pyroesp/PlayStation-1-Reset-Mod/pictures/arduino nano/arduino nano bottom.jpg

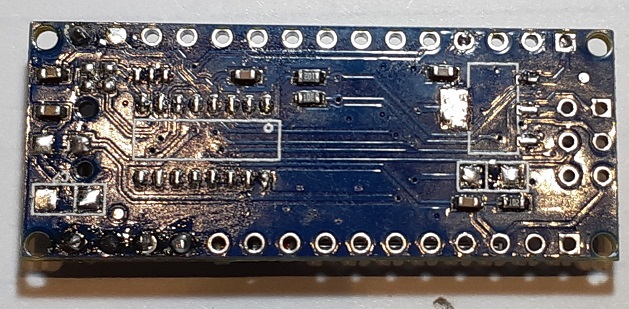
pictures/arduino nano/arduino nano bottom.jpg
