pyroesp/PlayStation-1-Reset-Mod/pictures/arduino nano/arduino nano top.jpg

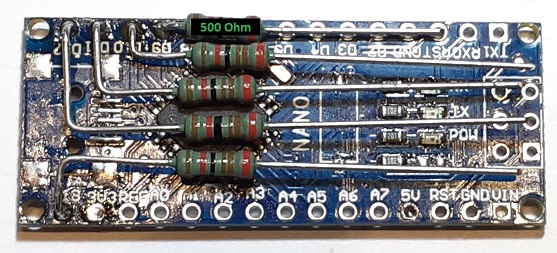
pictures/arduino nano/arduino nano top.jpg
