pyroesp/PlayStation-1-Reset-Mod/pictures/arduino nano/playstation with mod 2.jpg

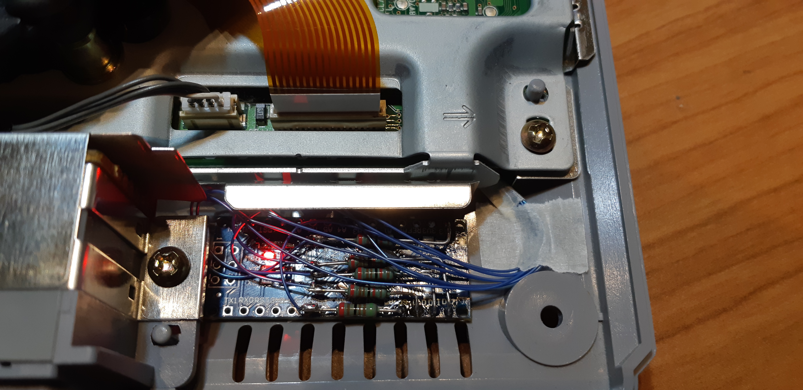
pictures/arduino nano/playstation with mod 2.jpg
