pyroesp/PlayStation-1-Reset-Mod/pictures/arduino nano/playstation with mod.jpg

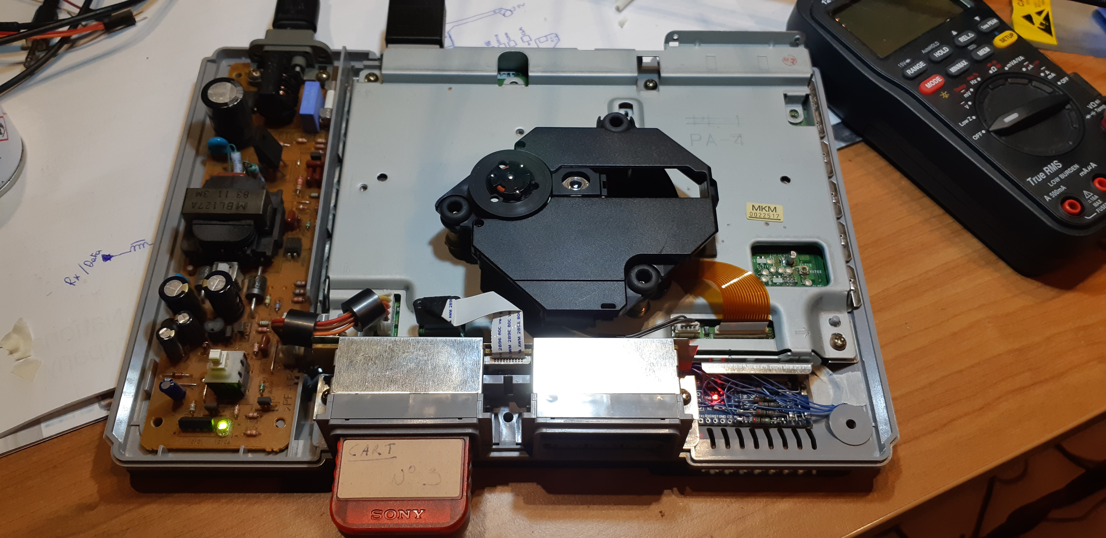
pictures/arduino nano/playstation with mod.jpg
