pyroesp/PlayStation-1-Reset-Mod/pictures/arduino nano/reset from parallel port.jpg

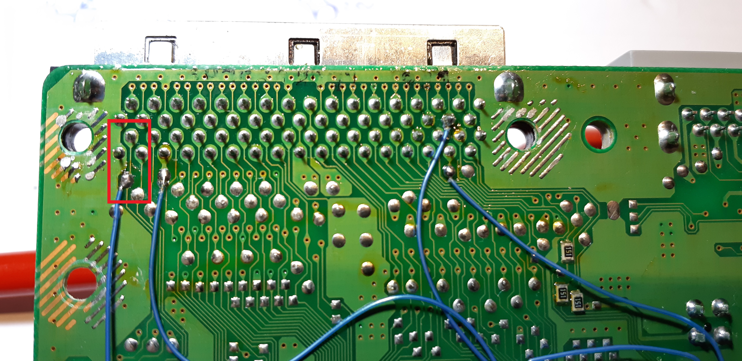
pictures/arduino nano/reset from parallel port.jpg
