pyroesp/PlayStation-1-Reset-Mod/pictures/mod/jlcpcb_parameters.PNG

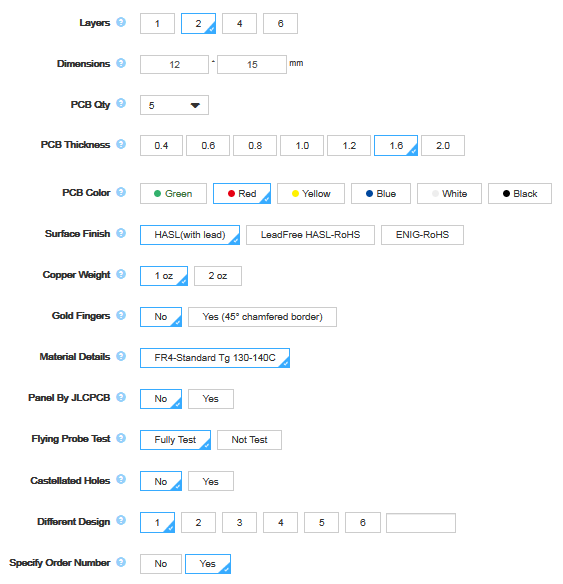
pictures/mod/jlcpcb_parameters.PNG
