pyroesp/PlayStation-1-Reset-Mod/pictures/pulse extender/pulse extender scope.jpg

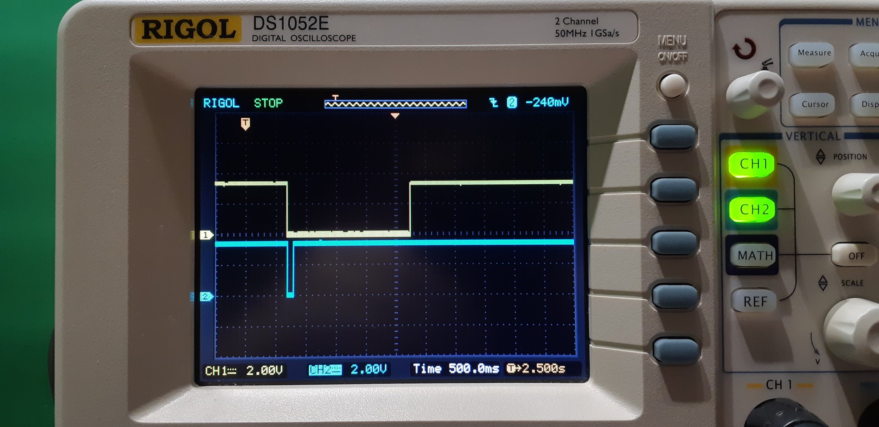
pictures/pulse extender/pulse extender scope.jpg
