pyroesp/PlayStation-1-Reset-Mod/pictures/guide/playstation-controller-pin-map.jpg

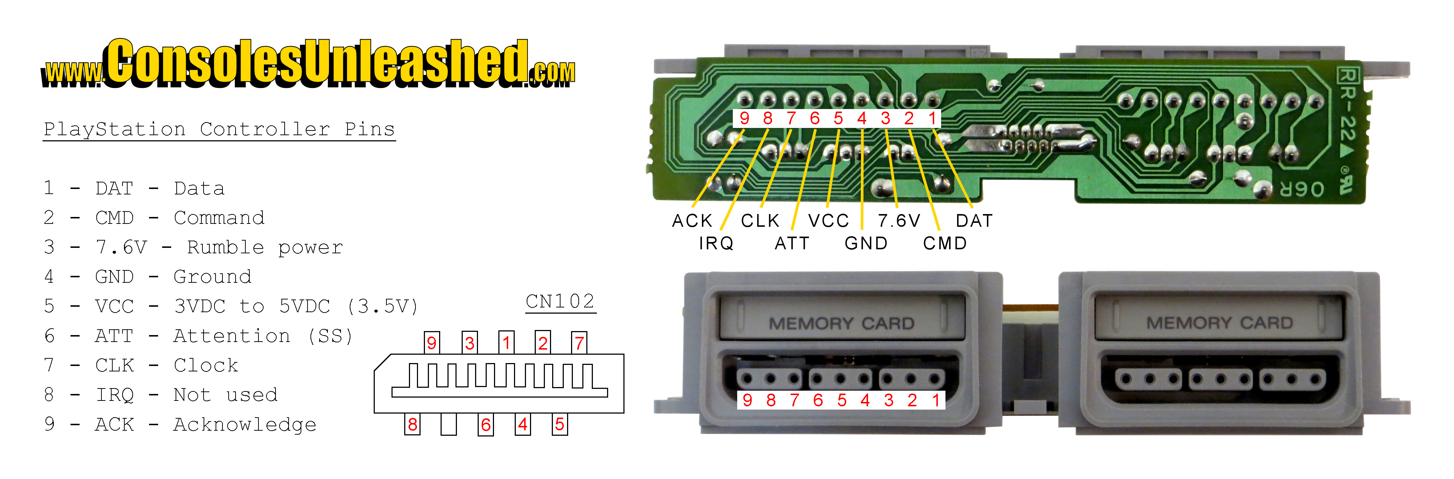
pictures/guide/playstation-controller-pin-map.jpg
