pyroesp/PlayStation-1-Reset-Mod/pictures/guide/playstation-igr-scph-100x-pu-8.jpg

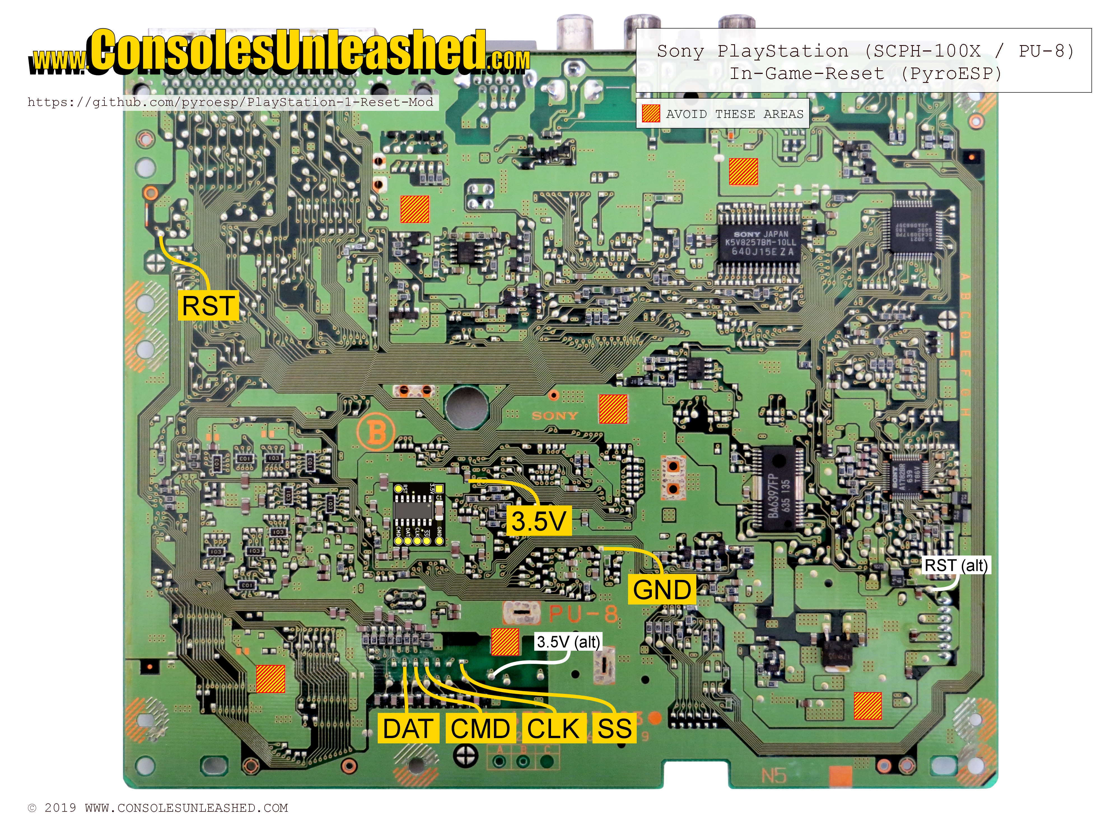
pictures/guide/playstation-igr-scph-100x-pu-8.jpg
