pyroesp/PlayStation-1-Reset-Mod/pictures/guide/playstation-igr-scph-550x-pu-18.jpg

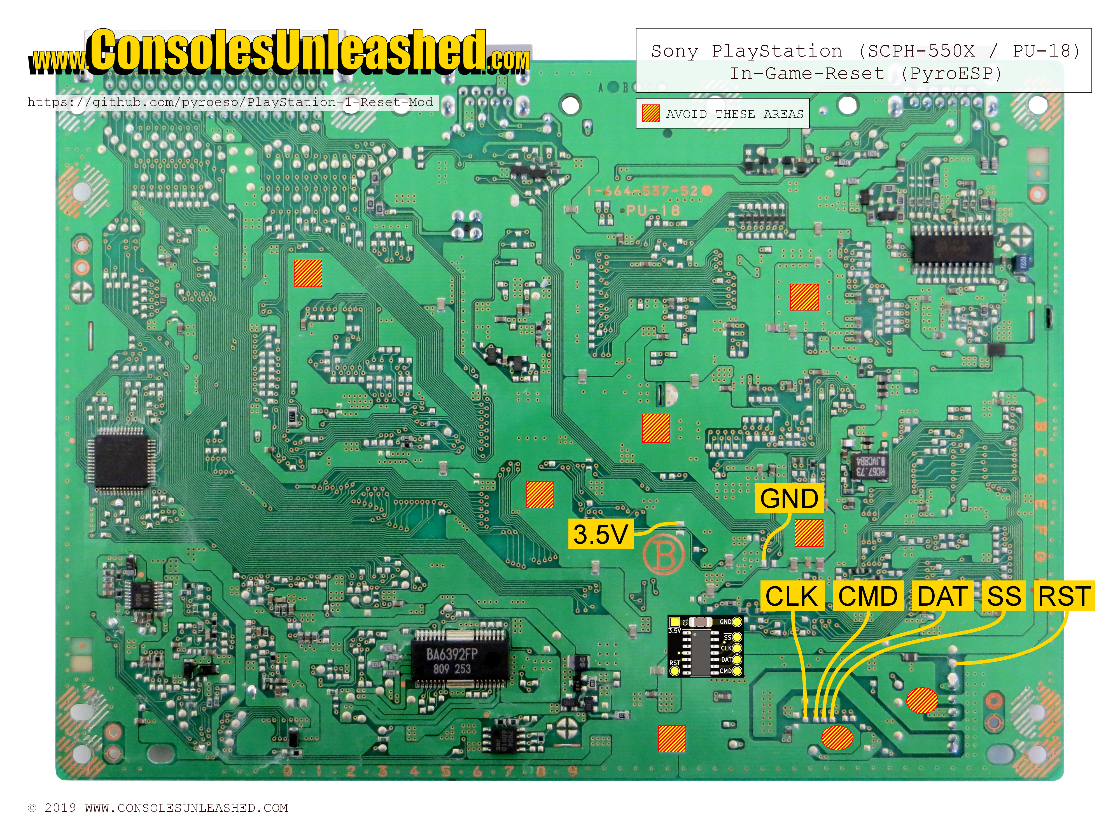
pictures/guide/playstation-igr-scph-550x-pu-18.jpg
