pyroesp/PlayStation-1-Reset-Mod/pictures/guide/playstation-igr-scph-750x-pu-22.jpg

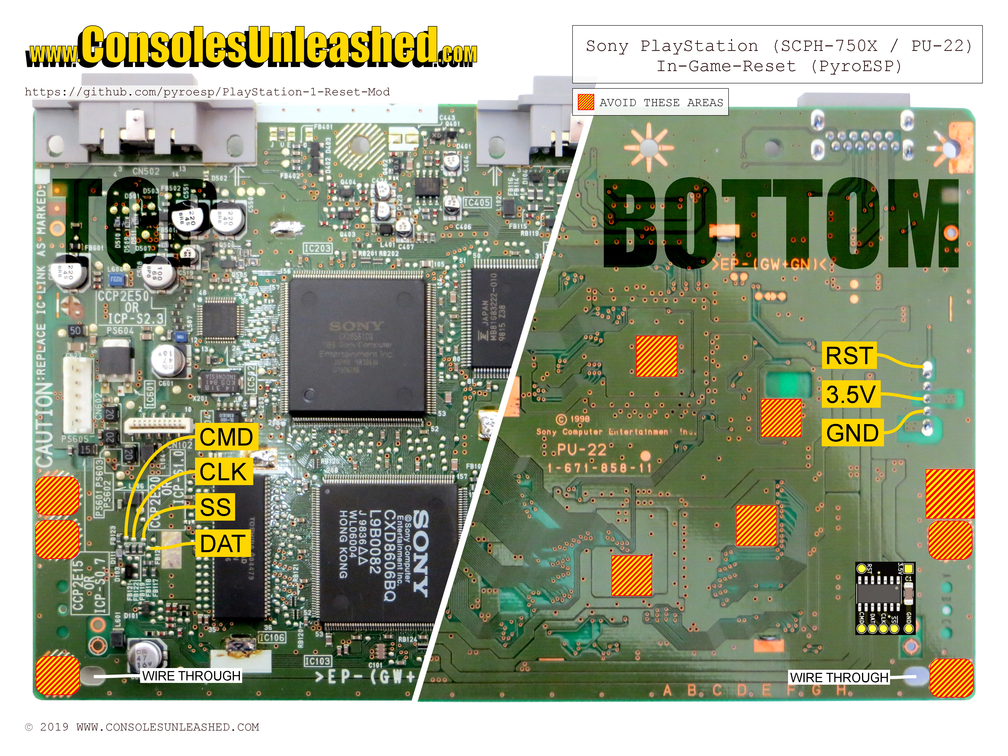
pictures/guide/playstation-igr-scph-750x-pu-22.jpg
