pyroesp/PlayStation-1-Reset-Mod/pictures/guide/playstation-igr-scph-900x-pu-23.jpg

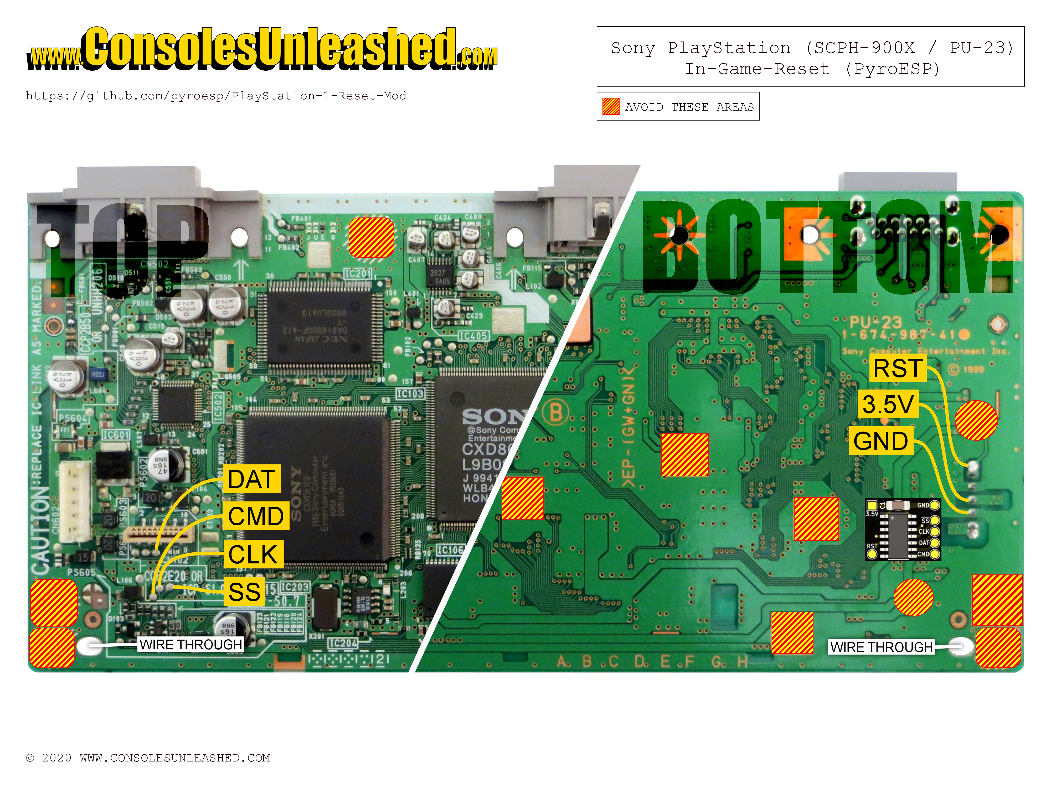
pictures/guide/playstation-igr-scph-900x-pu-23.jpg
